cole8888/SRNE-Solar-Charge-Controller-Monitor/Arduino-Example/Arduino-Nano-Closeup.jpg

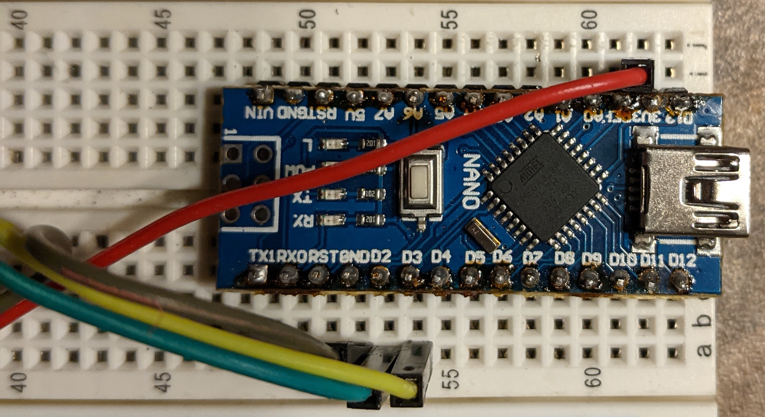
Arduino-Example/Arduino-Nano-Closeup.jpg
