cole8888/SRNE-Solar-Charge-Controller-Monitor/Arduino-Example/Cable-to-MAX3232-Breakout-Closeup.jpg

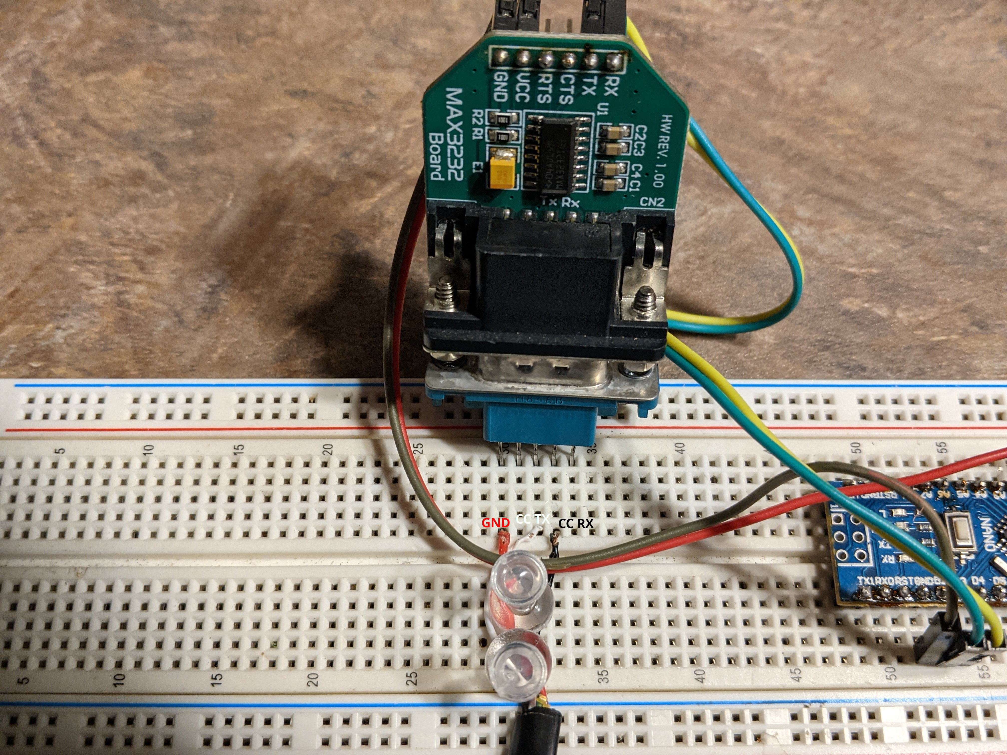
Arduino-Example/Cable-to-MAX3232-Breakout-Closeup.jpg
