cole8888/SRNE-Solar-Charge-Controller-Monitor/ESP32-Examples/6P6C-MAX3232.jpg

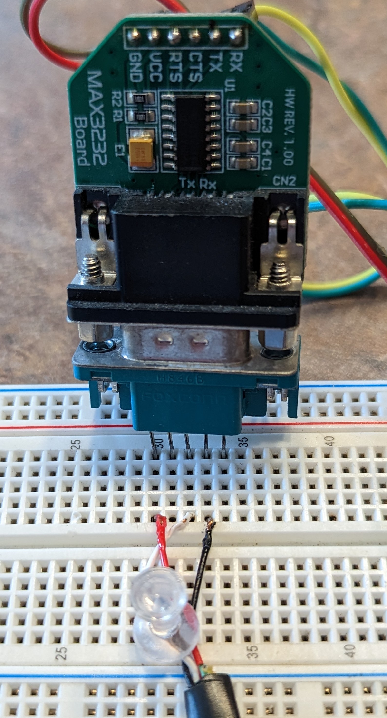
ESP32-Examples/6P6C-MAX3232.jpg
