cole8888/SRNE-Solar-Charge-Controller-Monitor/RaspberryPi-Examples/RaspberryPi-Cable-Connections-Close-Up.jpg

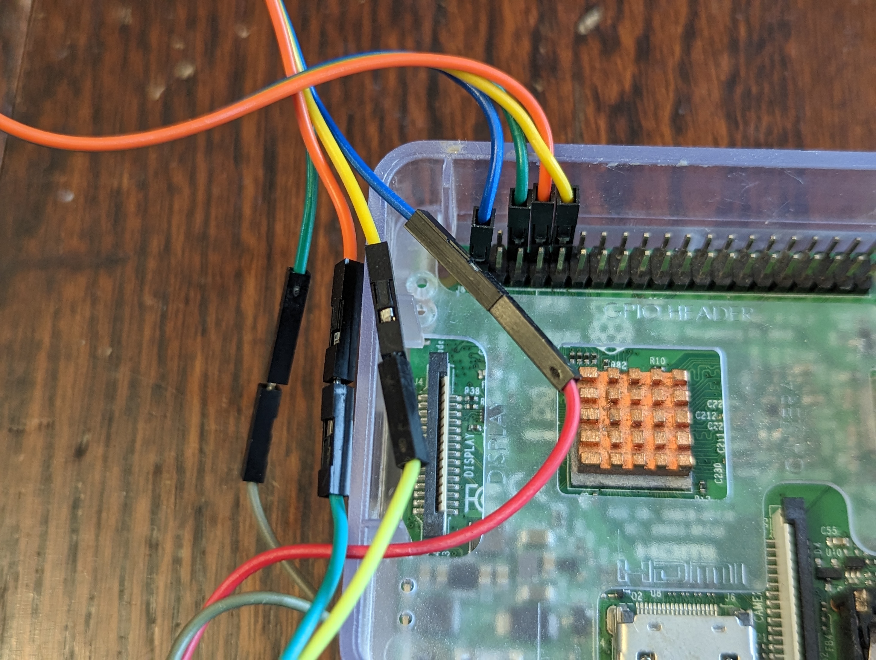
RaspberryPi-Examples/RaspberryPi-Cable-Connections-Close-Up.jpg
