cole8888/SRNE-Solar-Charge-Controller-Monitor/RaspberryPi-Examples/RaspberryPi-GPIO-Close-Up.jpg

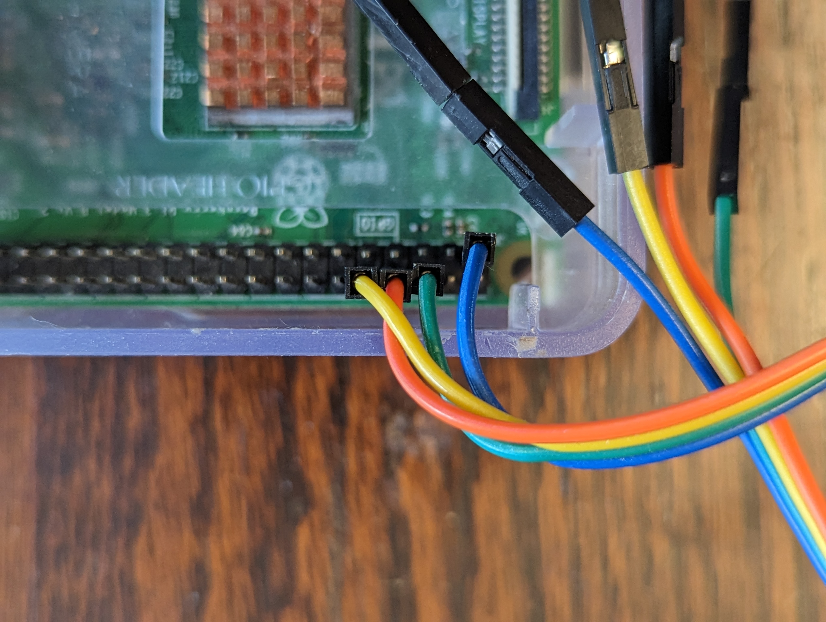
RaspberryPi-Examples/RaspberryPi-GPIO-Close-Up.jpg
