cole8888/SRNE-Solar-Charge-Controller-Monitor/RaspberryPi-Examples/RaspberryPi-Top-View.jpg

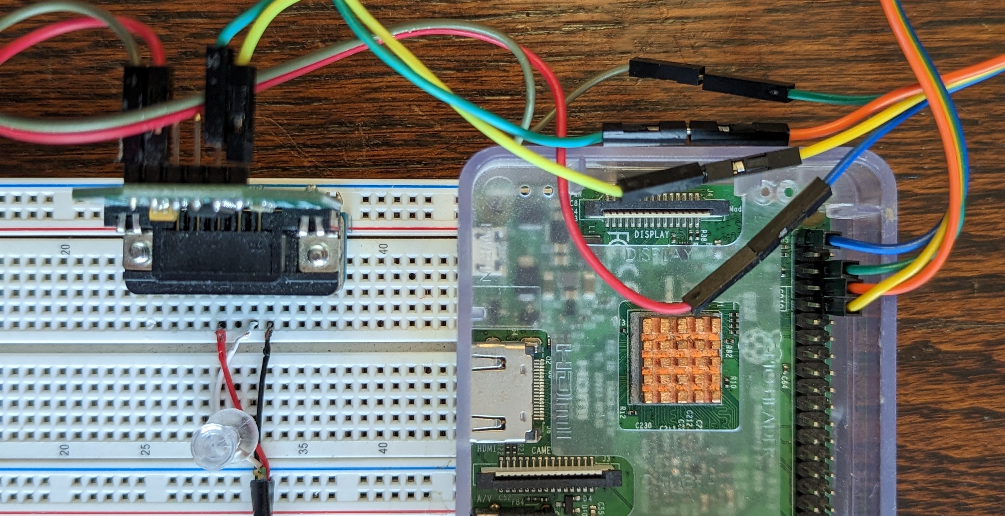
RaspberryPi-Examples/RaspberryPi-Top-View.jpg
